chrumck/bambu-chamber-heater/design/optocoupler.asc

M1: nmos; AON6264E
R1: res; 400
R2: res; 150
R3: res; 10k
U1: PC817A
V1: voltage; 12
V2: voltage; 5
V3: voltage; 3.3
Named nets: 0
.tran 1
