chrumck/bambu-chamber-heater/design/relayDriver.asc

M2: nmos; AON6264E
R2: res; 120
V1: voltage; 5
V2: voltage; 3.2
Named nets: 0
.tran 1
